CoolZeroNL/Marlin-Build/configuration/creality_cr10_s4_mks_mini_12864_v3/5.png

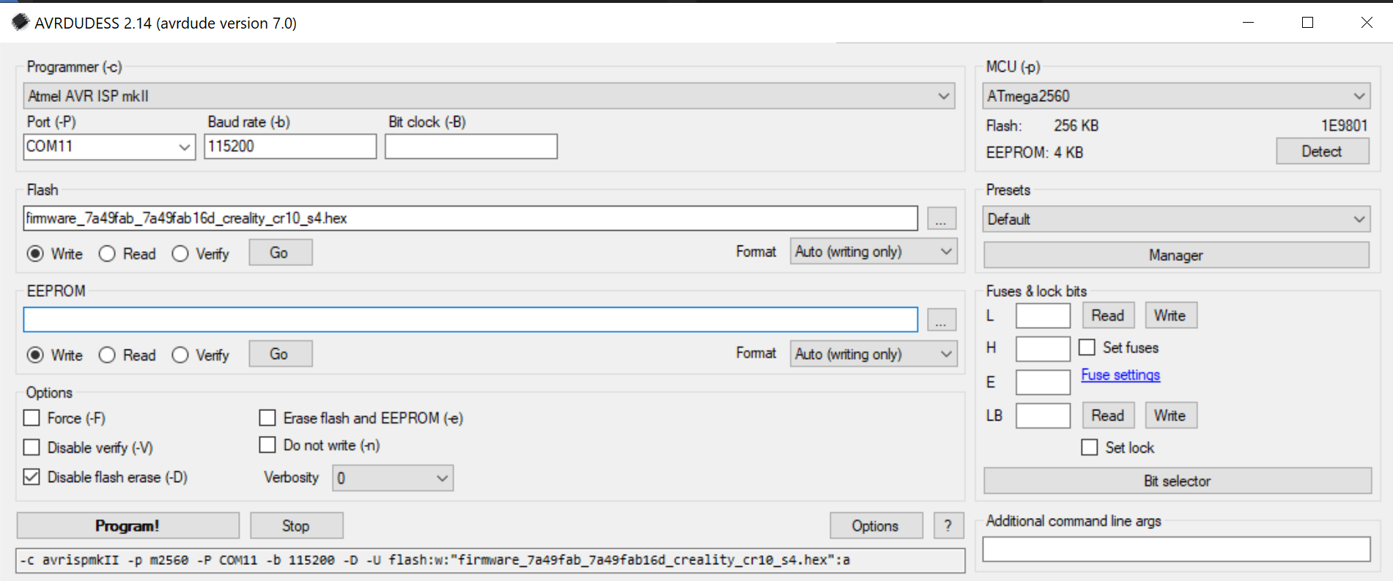
configuration/creality_cr10_s4_mks_mini_12864_v3/5.png
