CoolZeroNL/Marlin-Build/configuration/creality_cr10_s4_mks_mini_12864_v3/gCK_UjIfky1O9SxR03RogRuETqHudQwVys5JbvlcFKc.jpg

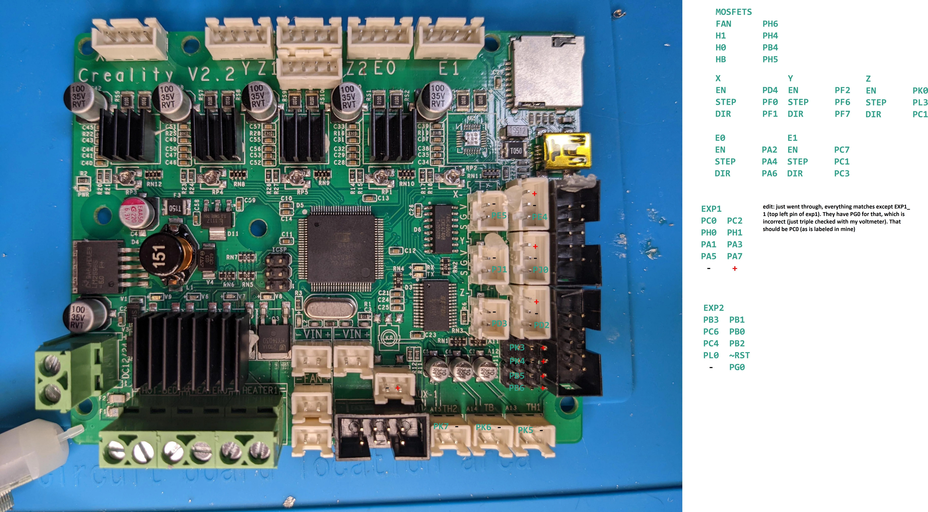
configuration/creality_cr10_s4_mks_mini_12864_v3/gCK_UjIfky1O9SxR03RogRuETqHudQwVys5JbvlcFKc.jpg
